Express1/STM32TFTClock/pictures/IMG_20201218_151808-4.jpg

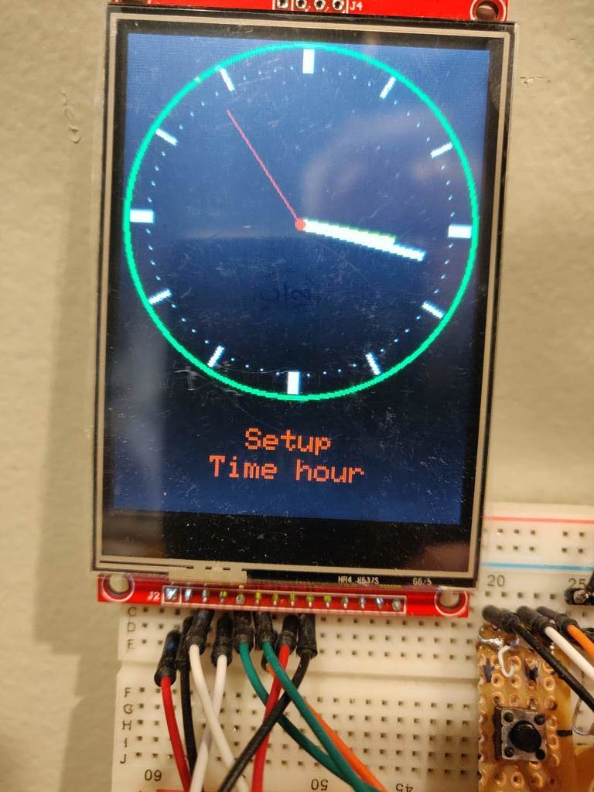
pictures/IMG_20201218_151808-4.jpg
