Express1/STM32TFTClock/pictures/IMG_20201218_151858-0.jpg

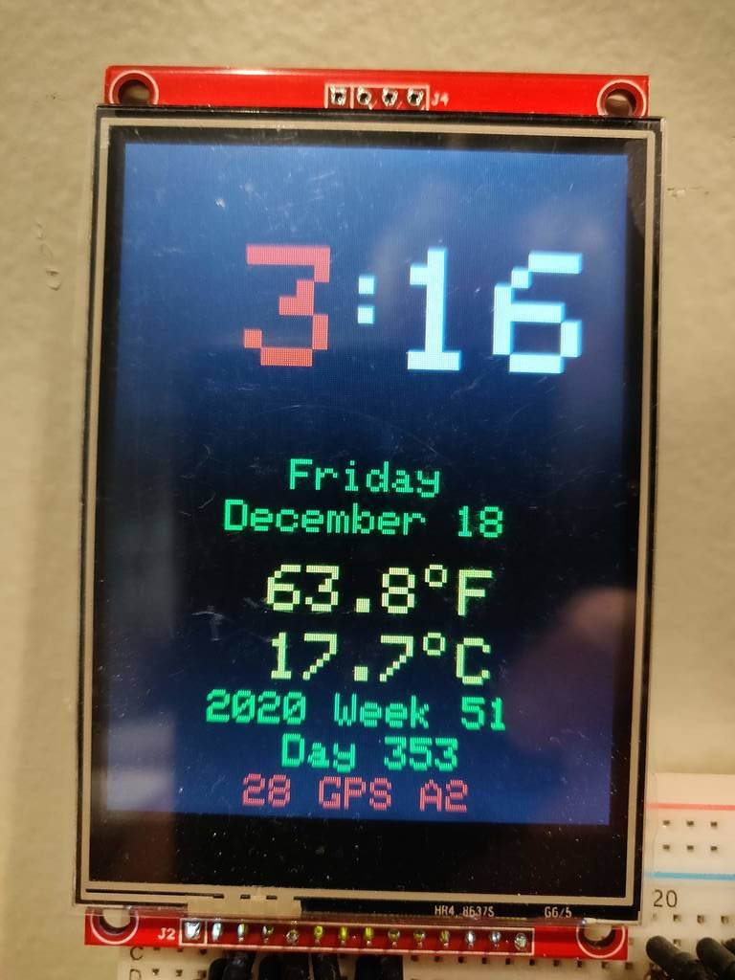
pictures/IMG_20201218_151858-0.jpg
