Express1/STM32TFTClock/pictures/IMG_20201218_151858-3.jpg

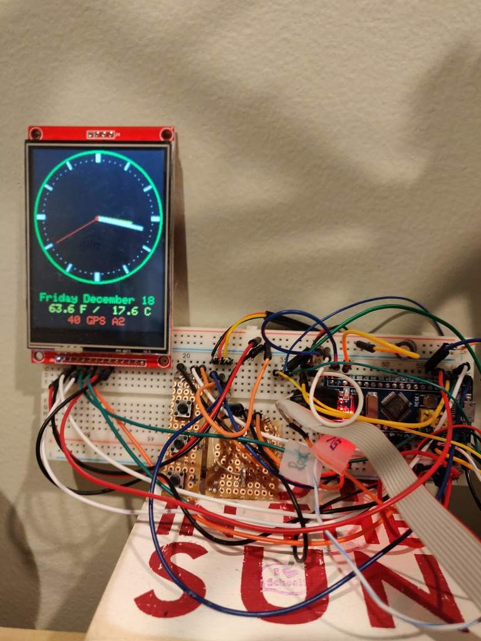
pictures/IMG_20201218_151858-3.jpg
